lusher00/Robust-IO/_claude_scratch/canarea.png

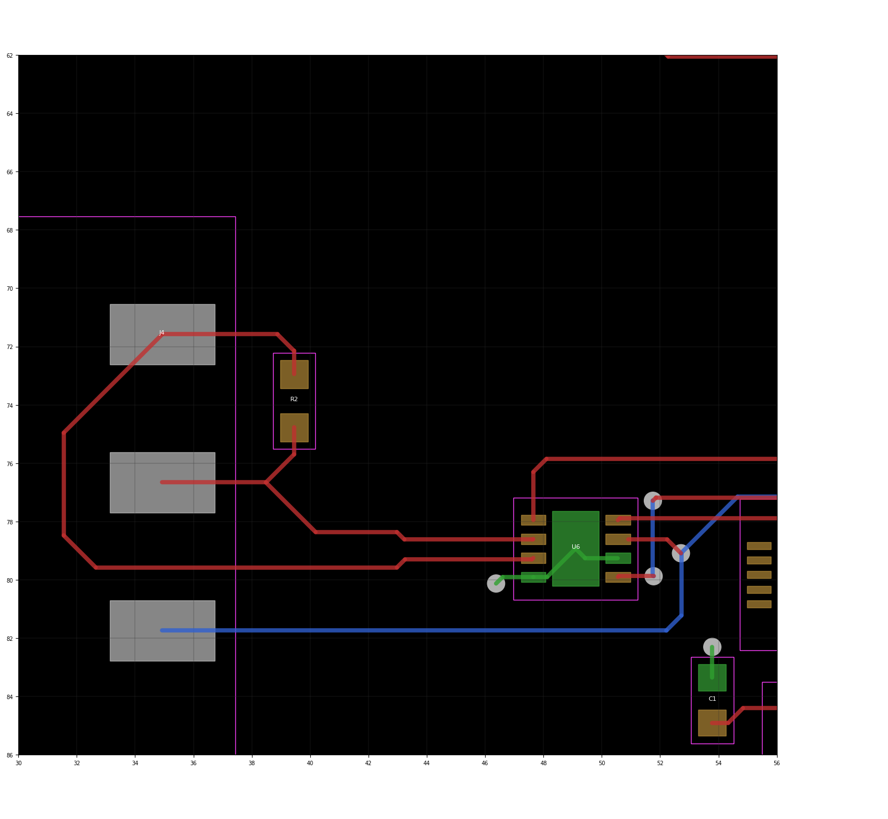
_claude_scratch/canarea.png
