lusher00/Robust-IO/_claude_scratch/capsA.png

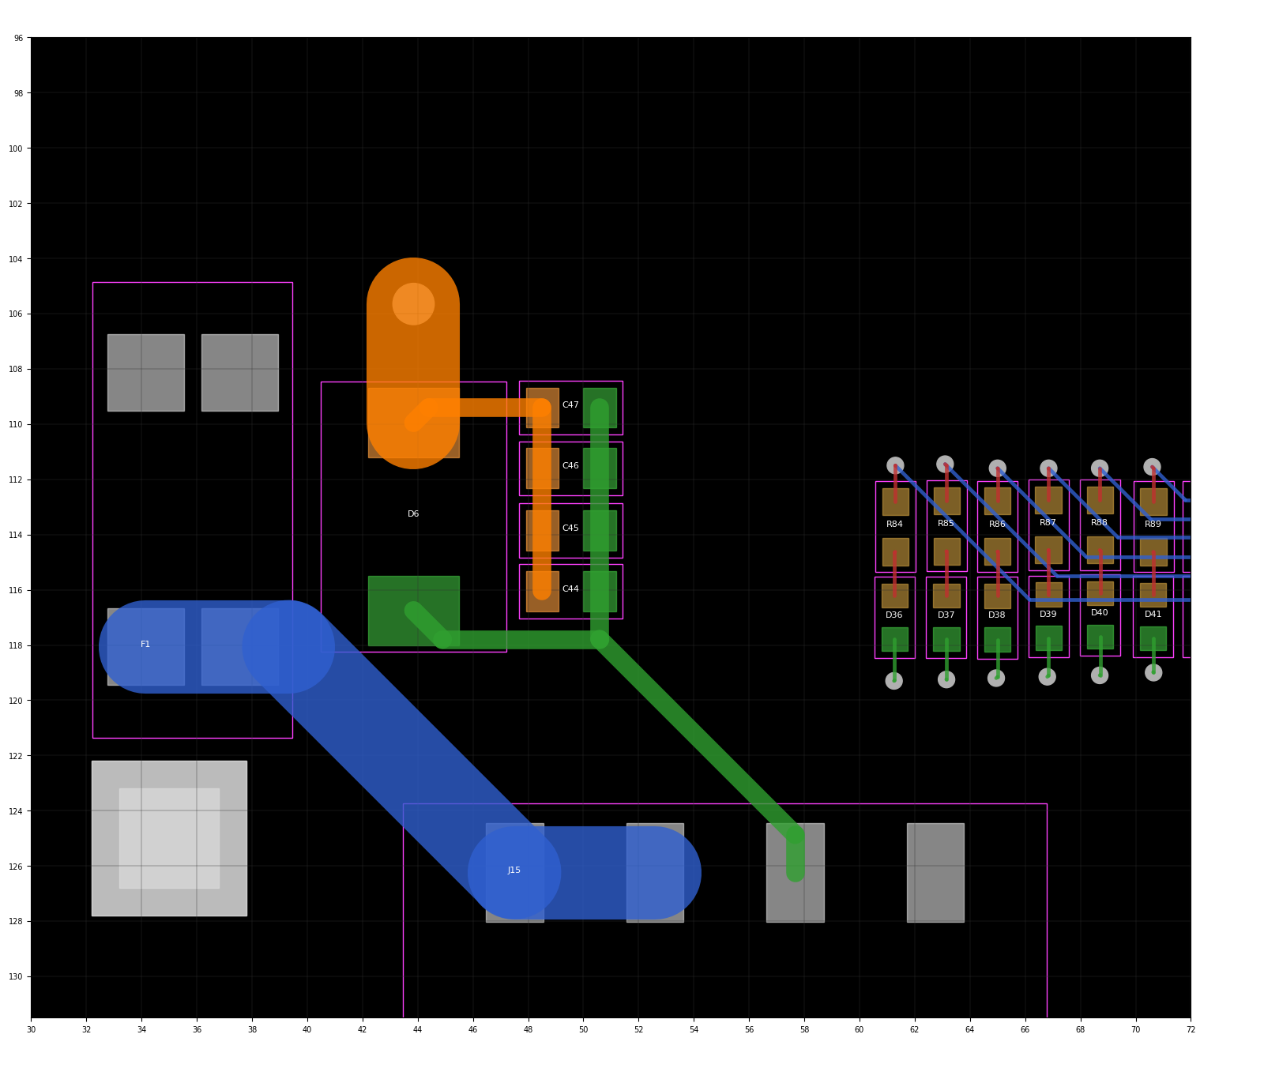
_claude_scratch/capsA.png
