lusher00/Robust-IO/_claude_scratch/capsB.png

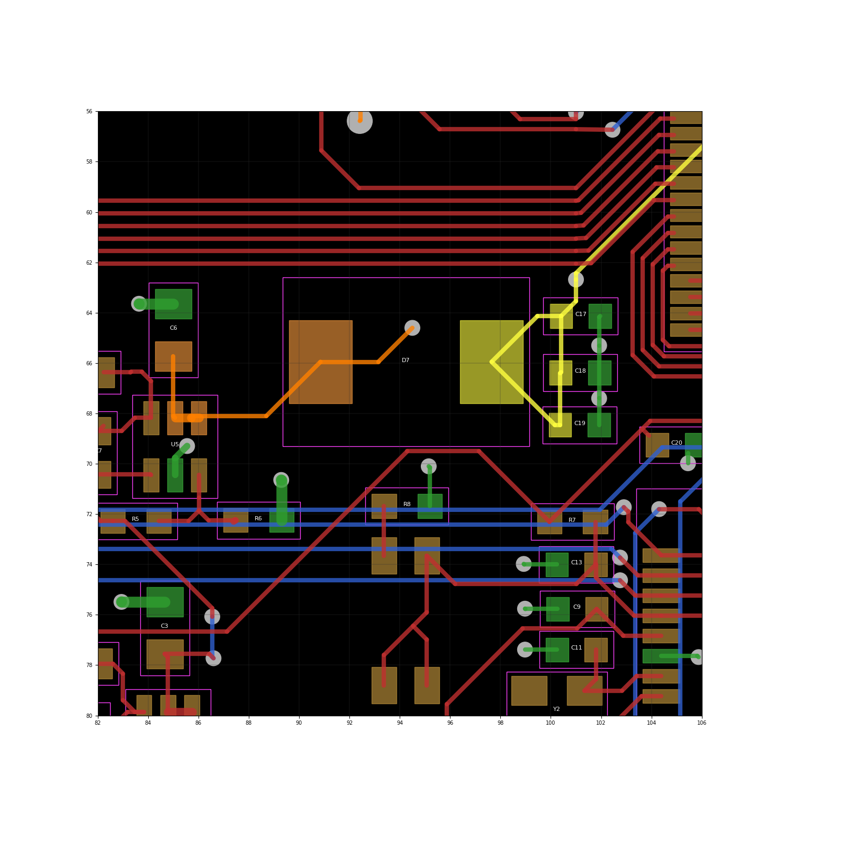
_claude_scratch/capsB.png
