lusher00/Robust-IO/_claude_scratch/dbg.png

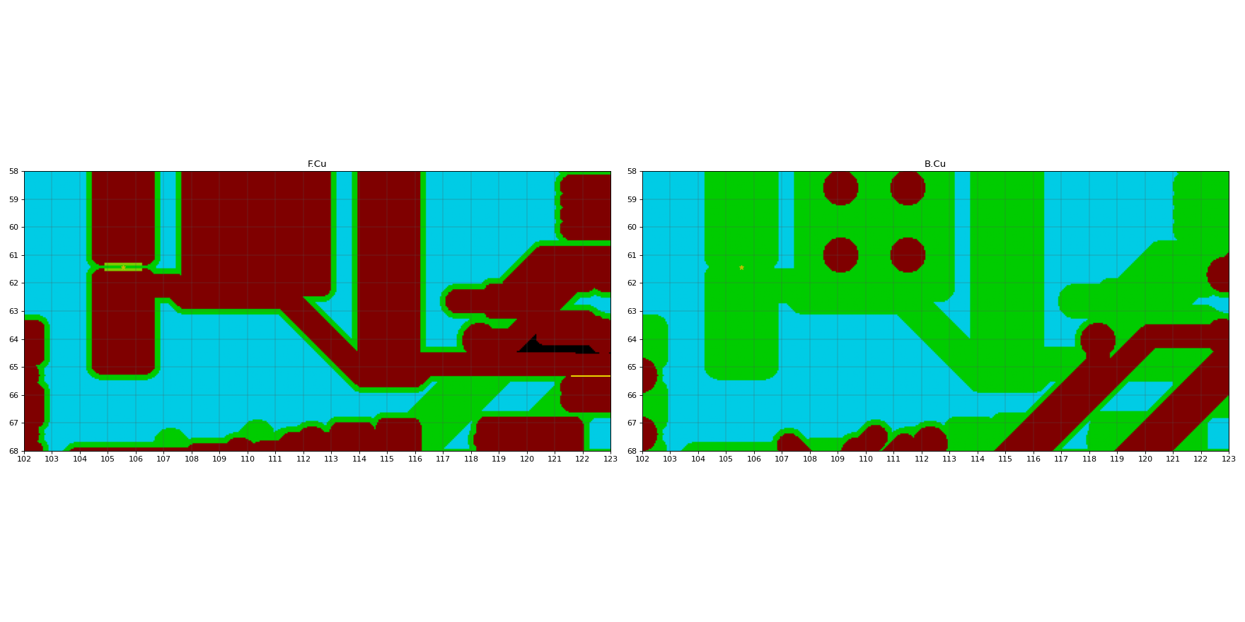
_claude_scratch/dbg.png
