lusher00/Robust-IO/_claude_scratch/plan.png

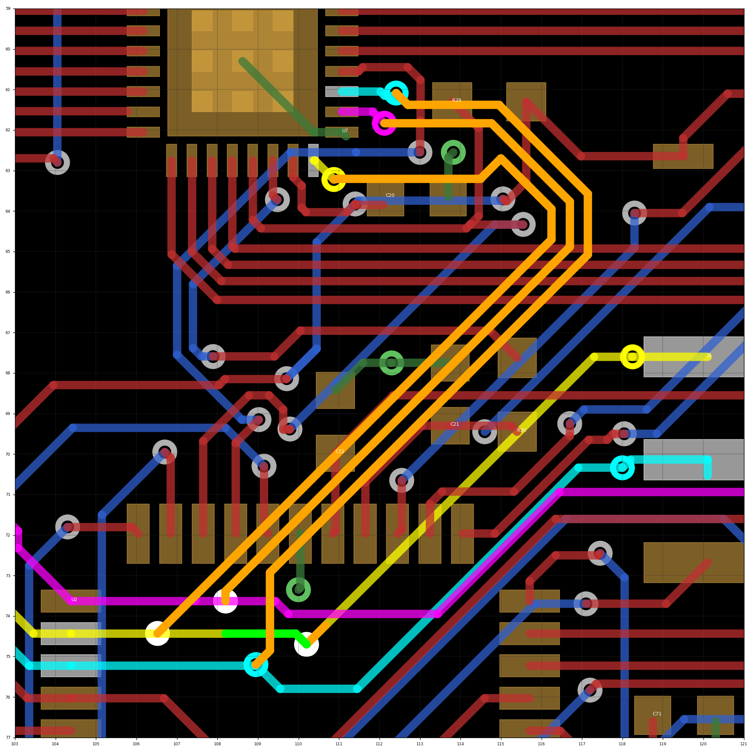
_claude_scratch/plan.png
