lusher00/Robust-IO/_claude_scratch/reach2.png

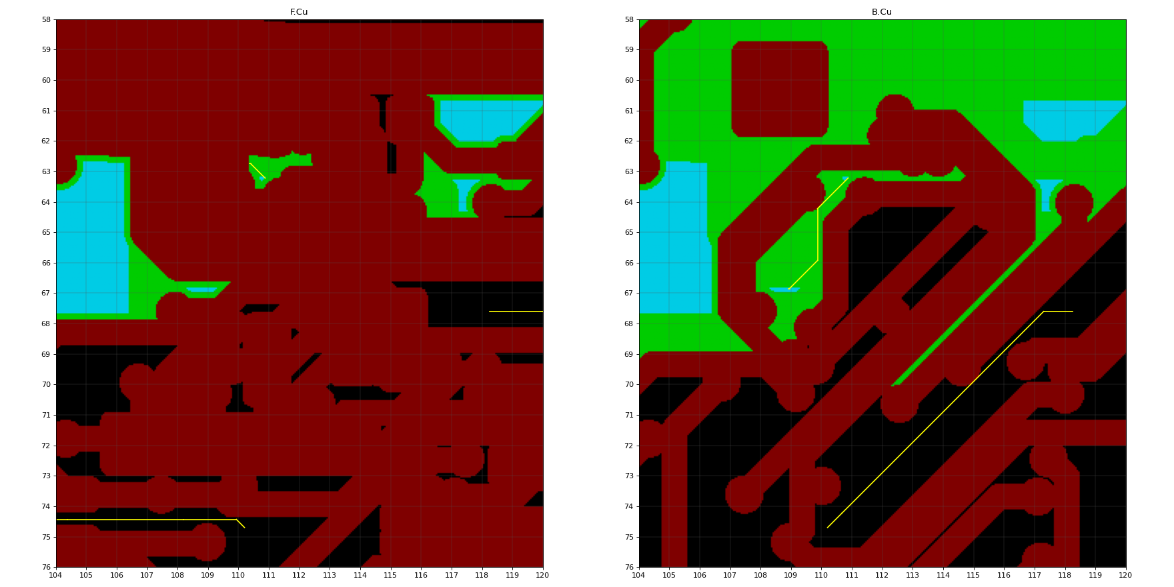
_claude_scratch/reach2.png
