lusher00/Robust-IO/_claude_scratch/reach_MISO0.png

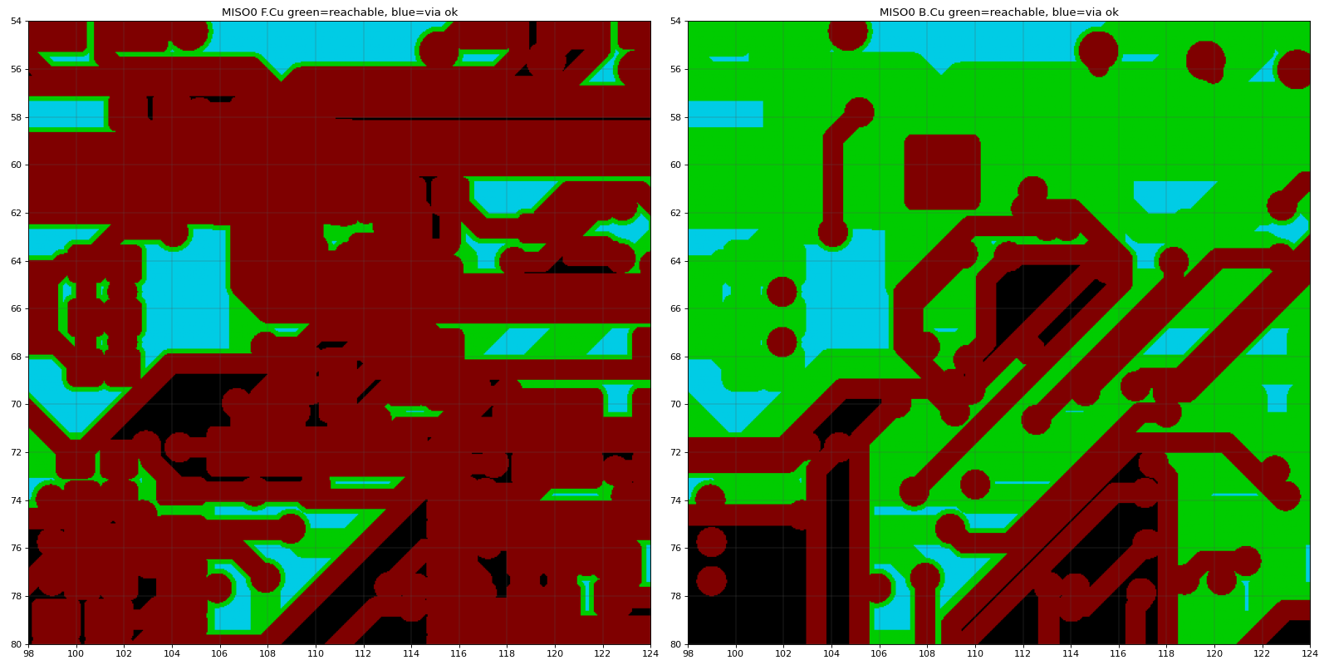
_claude_scratch/reach_MISO0.png
