lusher00/Robust-IO/_claude_scratch/reach_SCLK0.png

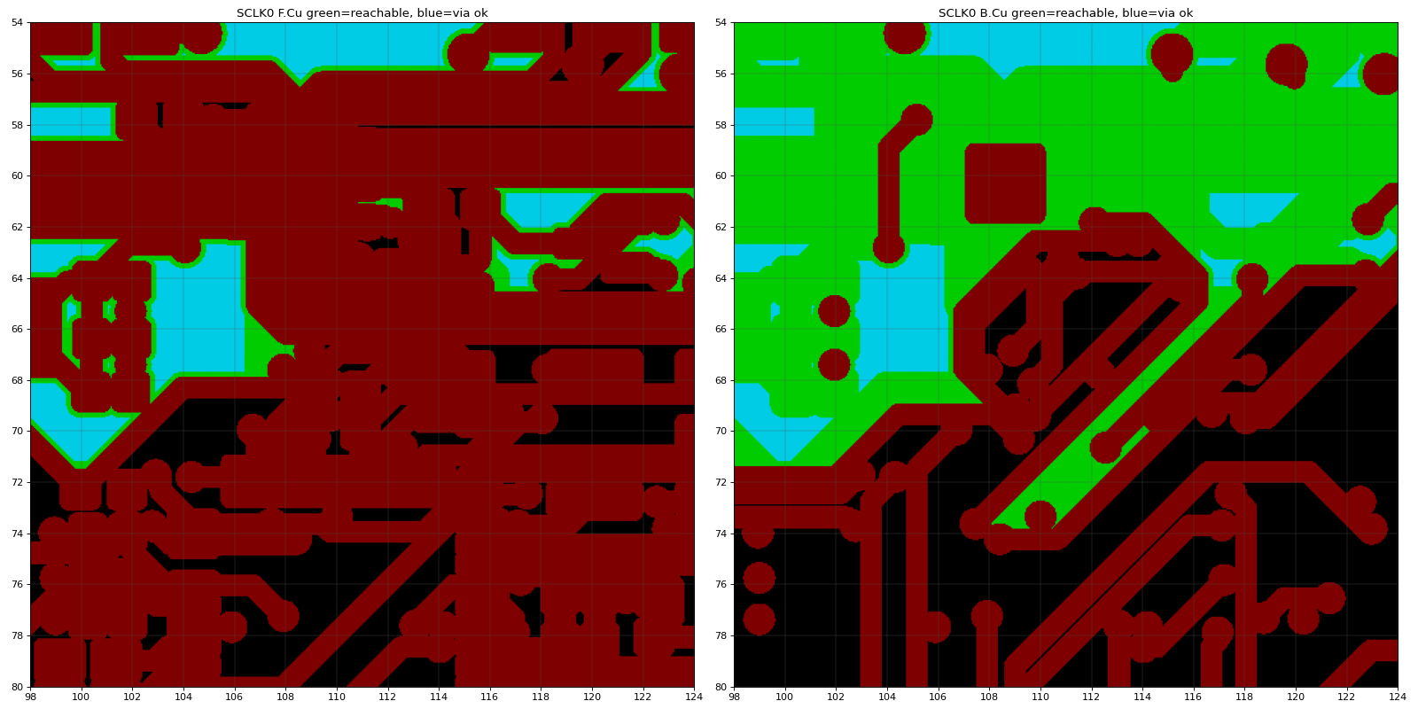
_claude_scratch/reach_SCLK0.png
