lusher00/Robust-IO/_claude_scratch/region.png

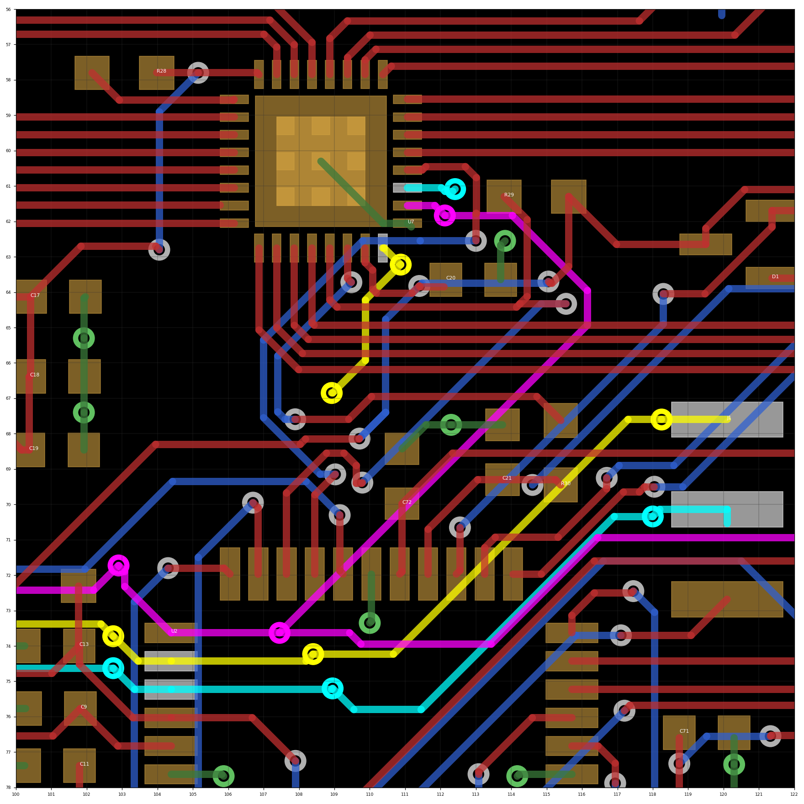
_claude_scratch/region.png
