lusher00/Robust-IO/_claude_scratch/u7final.png

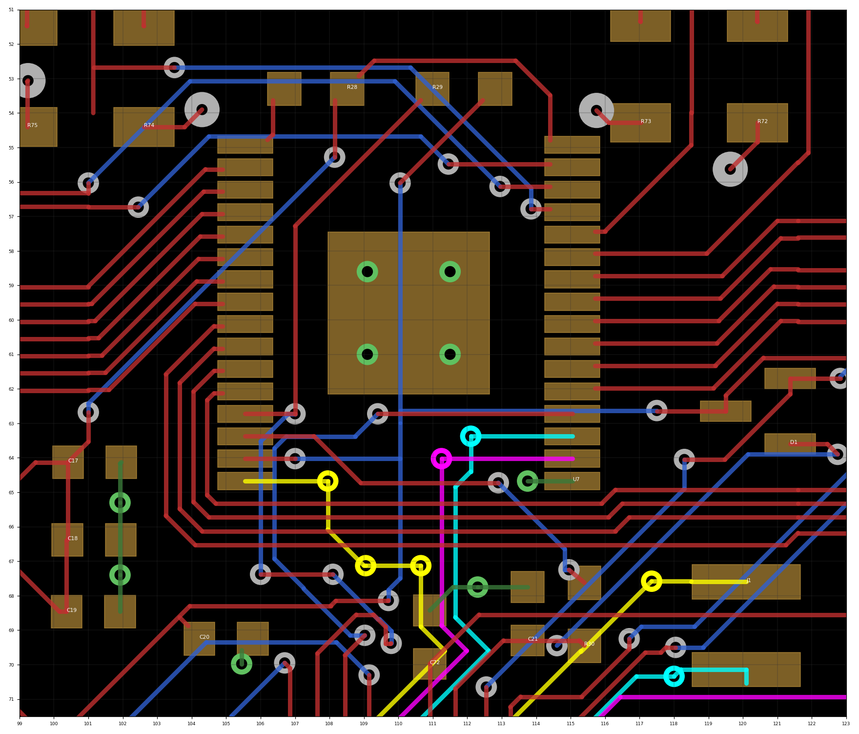
_claude_scratch/u7final.png
