lusher00/Robust-IO/_claude_scratch/u7r1.png

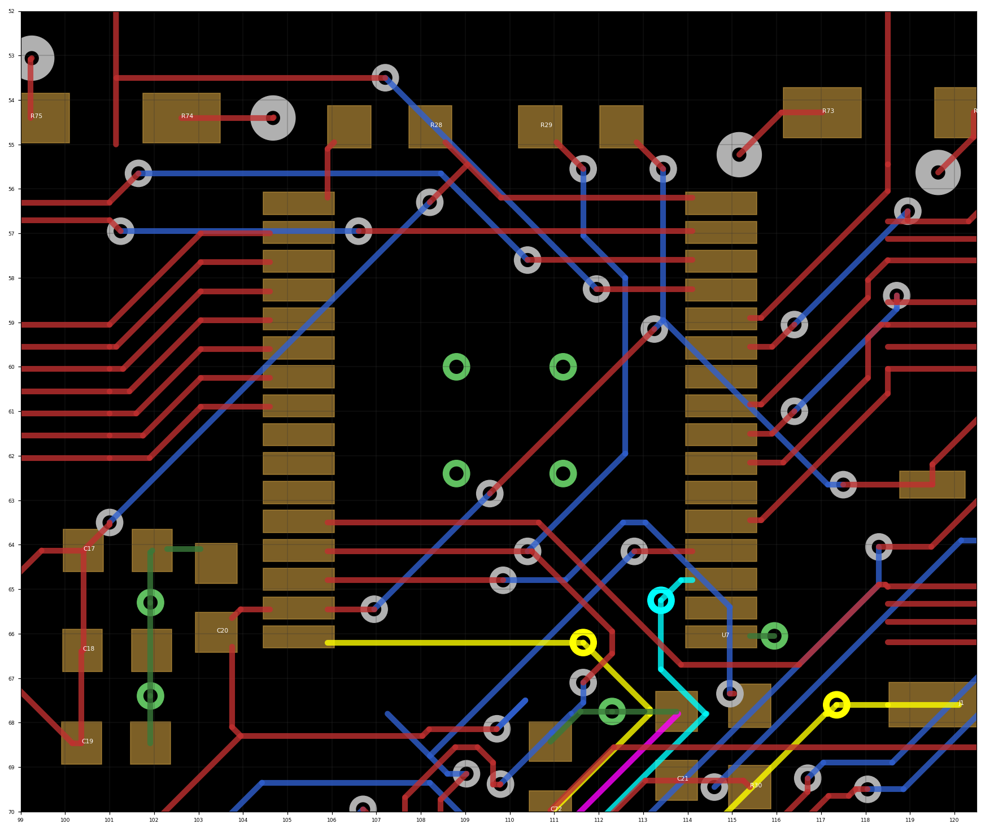
_claude_scratch/u7r1.png
