lusher00/Robust-IO/_claude_scratch/u7r2.png

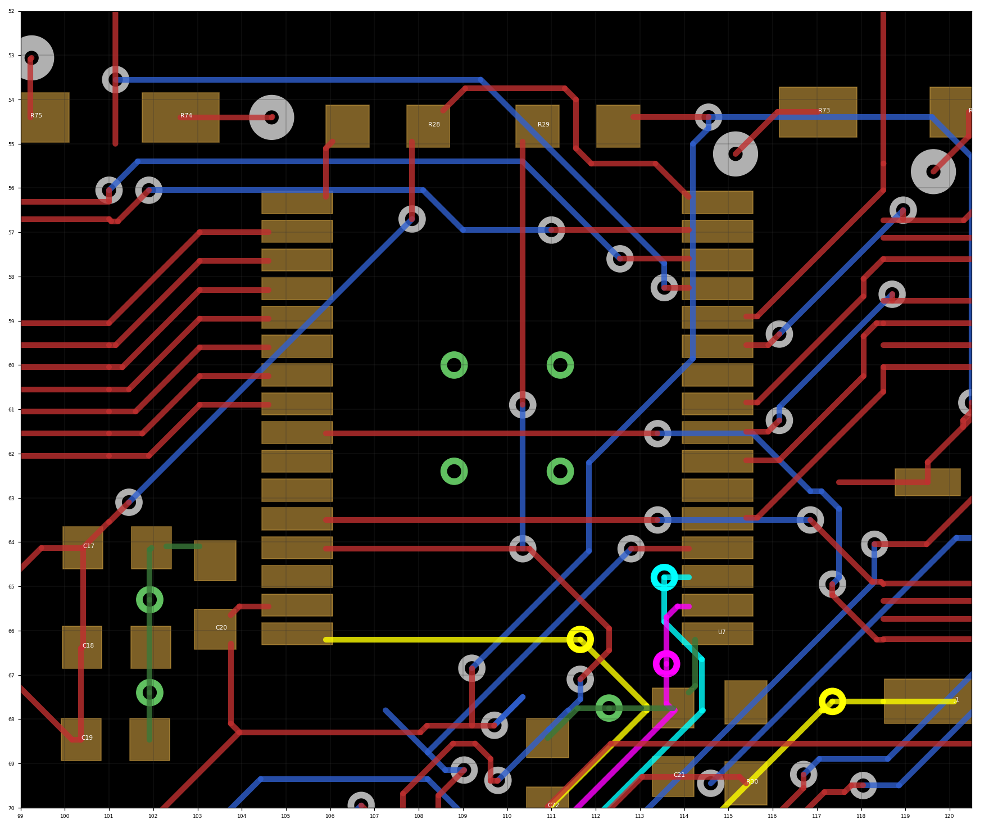
_claude_scratch/u7r2.png
