lusher00/Robust-IO/_claude_scratch/u7r3.png

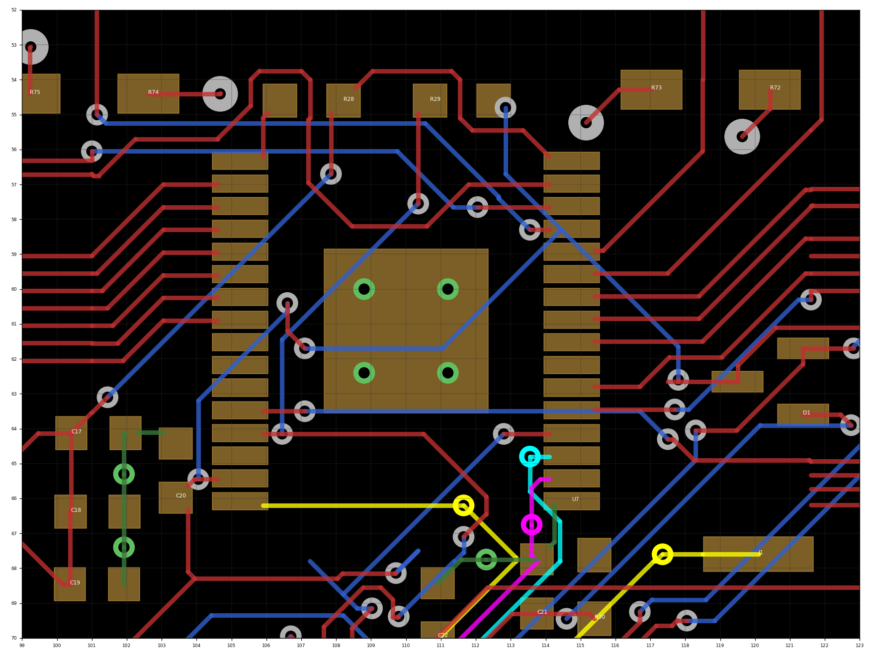
_claude_scratch/u7r3.png
