lusher00/Robust-IO/_claude_scratch/u7r5.png

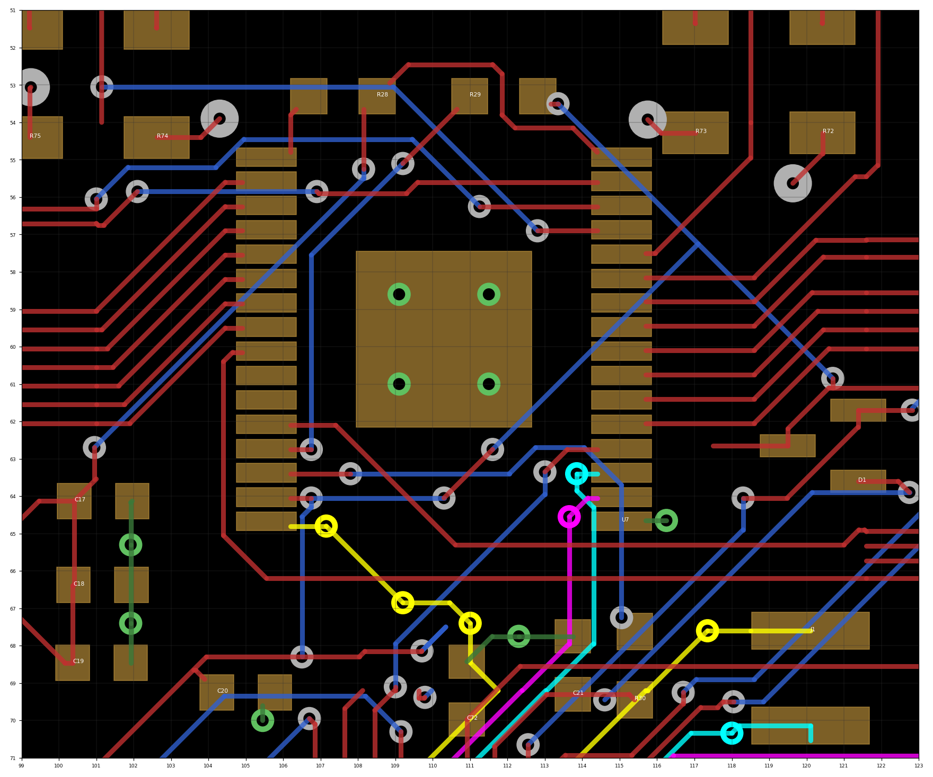
_claude_scratch/u7r5.png
