lusher00/Robust-IO/_claude_scratch/u7r10.png

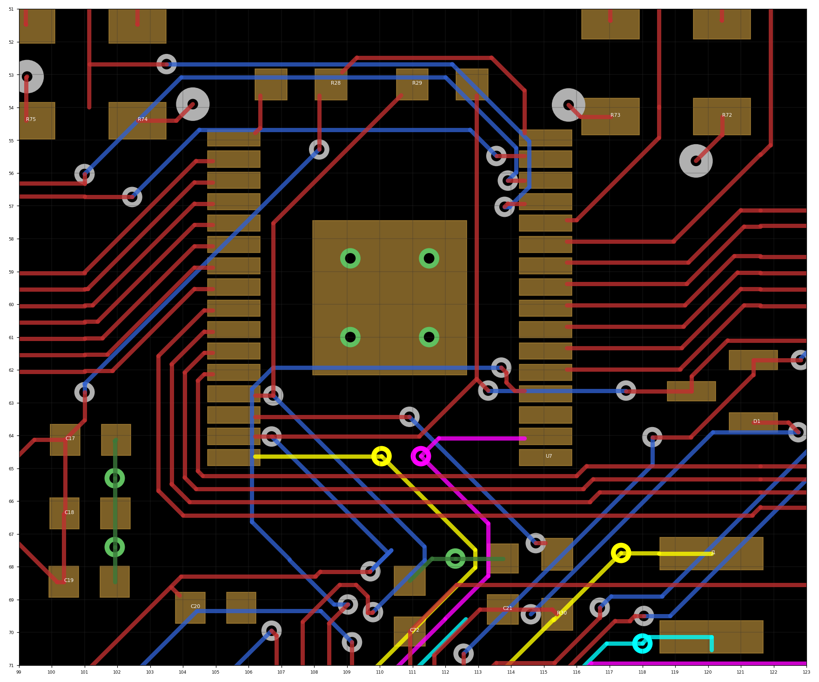
_claude_scratch/u7r10.png
