lusher00/Robust-IO/_claude_scratch/u7r11.png

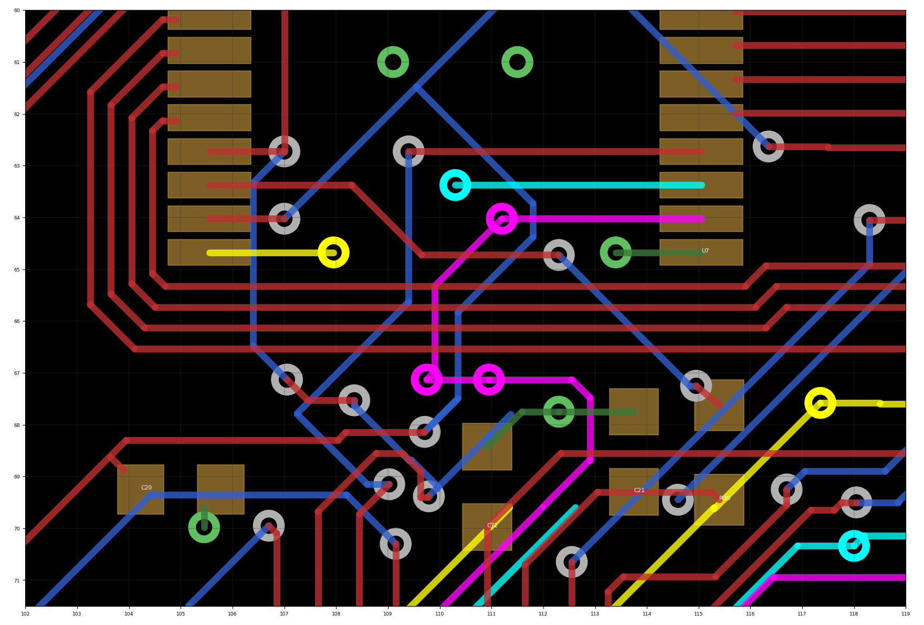
_claude_scratch/u7r11.png
