lusher00/Robust-IO/_claude_scratch/u7r13.png

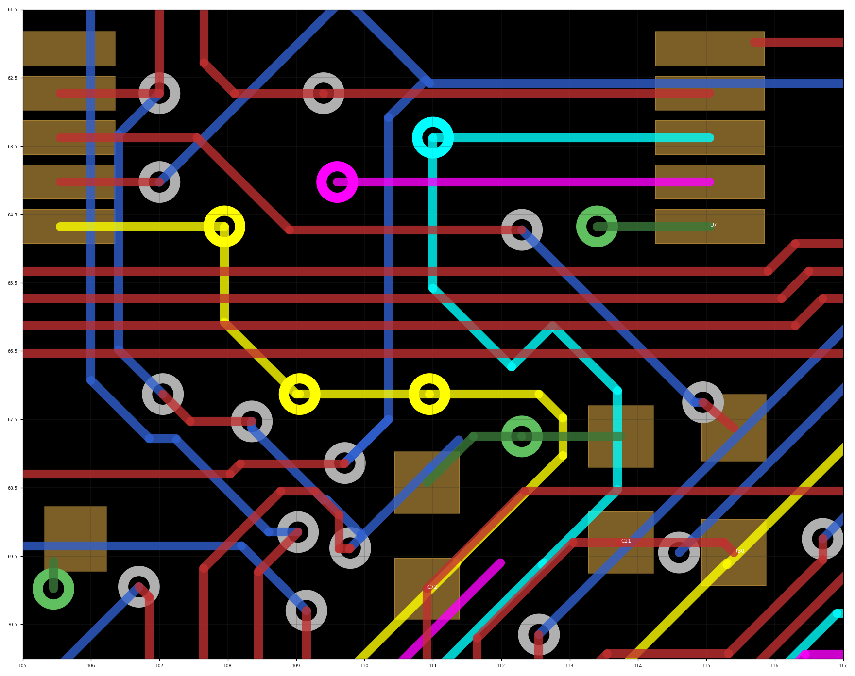
_claude_scratch/u7r13.png
