lusher00/Robust-IO/_claude_scratch/u7stageA.png

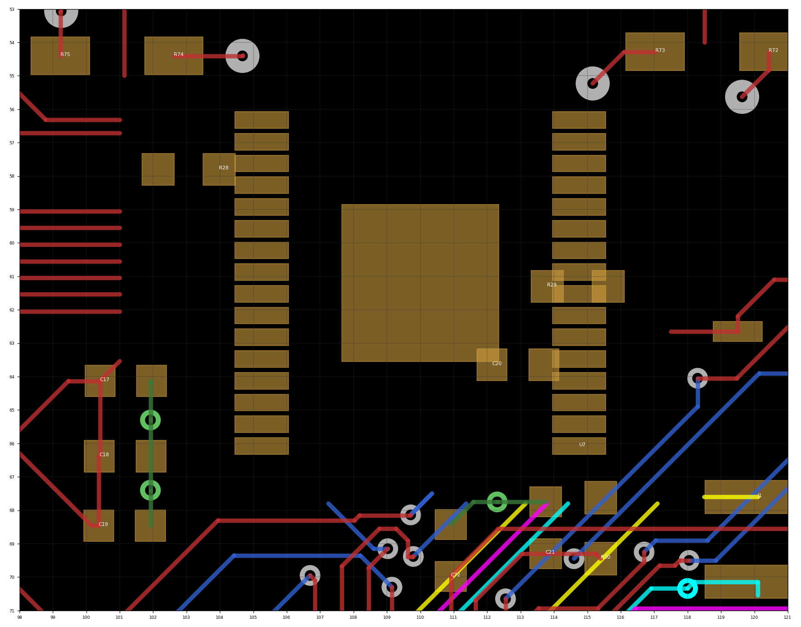
_claude_scratch/u7stageA.png
