lusher00/Robust-IO/_claude_scratch/uart_region.png

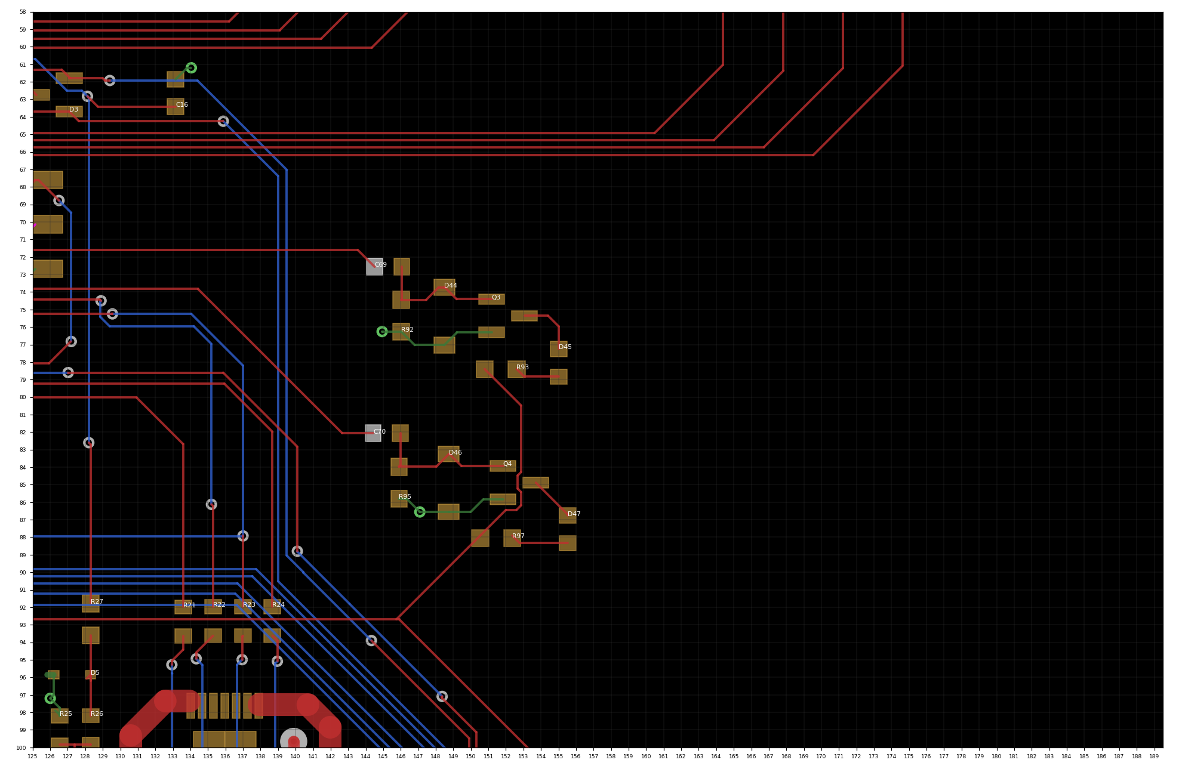
_claude_scratch/uart_region.png
