lusher00/Robust-IO/_claude_scratch/u7-soic-result.png

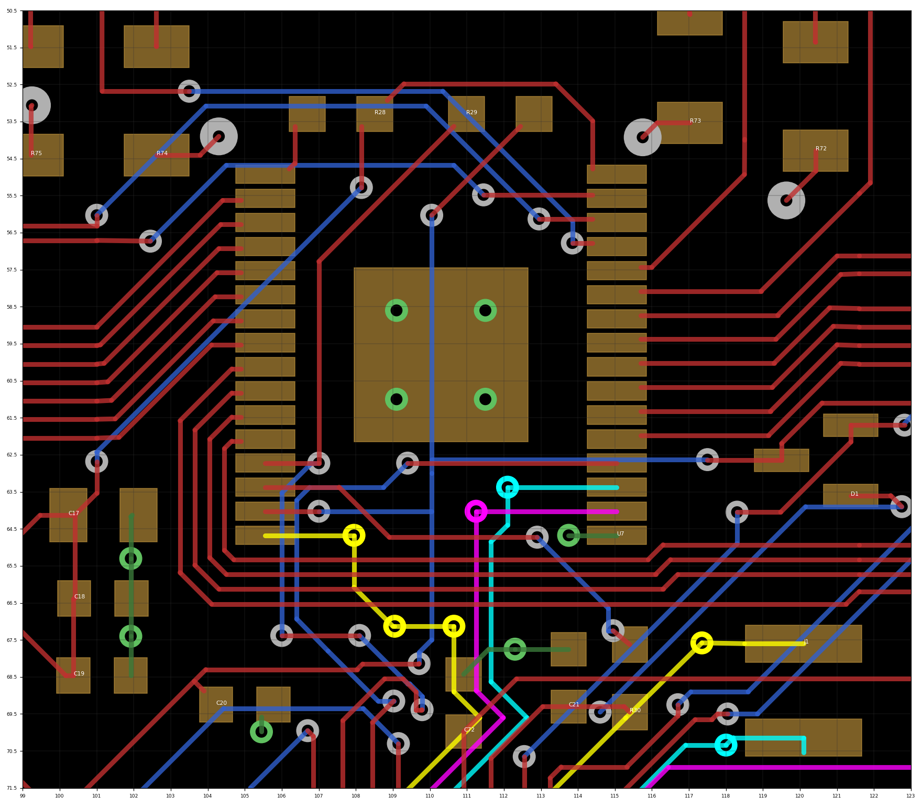
_claude_scratch/u7-soic-result.png
